zwenergy/CPAK2040/code/msc_disk.c

/*
 * The MIT License (MIT)
 *
 * Copyright (c) 2019 Ha Thach (tinyusb.org)
 *
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
 */
#include "hardware/gpio.h"
#include "bsp/board.h"
#include "tusb_config.h"
#include <stdio.h>

#include "hardware/flash.h"
#include "pico/time.h"


#define MEMPAKSIZE 32768
#define NRMEMPAKS 10
#define BASEMEMPAKADDR ( XIP_BASE + PICO_FLASH_SIZE_BYTES - ( NRMEMPAKS * MEMPAKSIZE ) )
#define MINMOUNTTIME_MS 5000

void writeMemPakToFlash( uint8_t* pak );
extern volatile uint8_t memPakCntr;
extern uint32_t usbReadMode;
void doBlinkPattern( uint32_t count );

// Flag for when a full write happened.
uint32_t fullUSBWriteDone = 0;

#if CFG_TUD_MSC

// whether host does safe-eject
static bool ejected = false;

enum
{
  DISK_BLOCK_NUM_READ = 640,
  DISK_BLOCK_NUM_WRITE = 230,
  DISK_BLOCK_SIZE = 512
};

    // Table for USB READ.
    uint8_t msc_disk_read[5][DISK_BLOCK_SIZE] =
        {
            //------------- Block0: Boot Sector -------------//
            // byte_per_sector    = DISK_BLOCK_SIZE; fat12_sector_num_16  = DISK_BLOCK_NUM;
            // sector_per_cluster = 1; reserved_sectors = 1;
            // fat_num            = 1; fat12_root_entry_num = 16;
            // sector_per_fat     = 1; sector_per_track = 1; head_num = 1; hidden_sectors = 0;
            // drive_number       = 0x80; media_type = 0xf8; extended_boot_signature = 0x29;
            // filesystem_type    = "FAT12   "; volume_serial_number = 0x1234; volume_label = "TinyUSB MSC";
            // FAT magic code at offset 510-511
            {
                // 0,0
                0xEB, 0x3C, 0x90,                               // 0 -2 jump code
                0x4D, 0x53, 0x44, 0x4F, 0x53, 0x35, 0x2E, 0x30, // 3- 10 MSDOS5.0
                0x00, 0x02,                                     // 11-12 BYTES PER SECTOR
                0x04,                                           // 13 SECTORS PER CLUSTER
                0x01, 0x00,                                     // 14-15 Number of reserved sectors
                0x01,                                           // 16 Number of FATs
                0x10, 0x00,                                     // 17-18 max number of root directory enteries
                0x00, 0x20,                                     // 19-20 total number of sectors (set 0 and use 32-35 if large)
                0xF8,                                           // 21 IGNORE
                0x01, 0x00,                                     // 22-23 Sectors per fat
                0x01, 0x00,                                     // 24-25 sectors per track
                0x01, 0x00,                                     // 26-27 number of heads
                0x00, 0x00, 0x00, 0x00,                         // 28-31 IGNORE
                0x00, 0x00, 0x00, 0x00,                         // 32-35 total number of sectors for FAT32, fat 12 and 16 ignore
                0x80,                                           // 36 drive number, IGNORE
                0x00,                                           // 37 IGNORE
                0x29,                                           // 38 This inidicates the next few identifying fields are pressent
                0x34, 0x12, 0x00, 0x00,                         // 39-42 serial number
                'T', 'i', 'n', 'y', 'U',
                'S', 'B', ' ', 'M', 'S', 'C', // 43-53 volume ID

                0x46, 0x41, 0x54, 0x31, 0x32, 0x20, 0x20, 0x20, // 54-61 FILE SYSTEM TYPE (FAT12, FAT16 etc)
                0x00, 0x00,                                     // 62-509 "unused"

                // Zero up to 2 last bytes of FAT magic code
                0x00, 0x00, 0x00, 0x00, 0x00, 0x00, 0x00, 0x00, 0x00, 0x00, 0x00, 0x00, 0x00, 0x00, 0x00, 0x00,
                0x00, 0x00, 0x00, 0x00, 0x00, 0x00, 0x00, 0x00, 0x00, 0x00, 0x00, 0x00, 0x00, 0x00, 0x00, 0x00,
                0x00, 0x00, 0x00, 0x00, 0x00, 0x00, 0x00, 0x00, 0x00, 0x00, 0x00, 0x00, 0x00, 0x00, 0x00, 0x00,
                0x00, 0x00, 0x00, 0x00, 0x00, 0x00, 0x00, 0x00, 0x00, 0x00, 0x00, 0x00, 0x00, 0x00, 0x00, 0x00,
                0x00, 0x00, 0x00, 0x00, 0x00, 0x00, 0x00, 0x00, 0x00, 0x00, 0x00, 0x00, 0x00, 0x00, 0x00, 0x00,
                0x00, 0x00, 0x00, 0x00, 0x00, 0x00, 0x00, 0x00, 0x00, 0x00, 0x00, 0x00, 0x00, 0x00, 0x00, 0x00,
                0x00, 0x00, 0x00, 0x00, 0x00, 0x00, 0x00, 0x00, 0x00, 0x00, 0x00, 0x00, 0x00, 0x00, 0x00, 0x00,
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
                0x00, 0x80, 0x00, 0x00, 

                'M', 'E', 'M', 'P', 'A', 'K', '0', '5', 'M', 'P', 'K', 0x20, 0x00, 0xC6, 0x52, 0x6D,
                0x65, 0x43, 0x65, 0x43, 0x00, 0x00, 0x88, 0x6D, 0x65, 0x43, 0x42, 0x00,
                0x00, 0x80, 0x00, 0x00, 

                'M', 'E', 'M', 'P', 'A', 'K', '0', '6', 'M', 'P', 'K', 0x20, 0x00, 0xC6, 0x52, 0x6D,
                0x65, 0x43, 0x65, 0x43, 0x00, 0x00, 0x88, 0x6D, 0x65, 0x43, 0x52, 0x00,
                0x00, 0x80, 0x00, 0x00, 

                'M', 'E', 'M', 'P', 'A', 'K', '0', '7', 'M', 'P', 'K', 0x20, 0x00, 0xC6, 0x52, 0x6D,
                0x65, 0x43, 0x65, 0x43, 0x00, 0x00, 0x88, 0x6D, 0x65, 0x43, 0x62, 0x00,
                0x00, 0x80, 0x00, 0x00, 

                'M', 'E', 'M', 'P', 'A', 'K', '0', '8', 'M', 'P', 'K', 0x20, 0x00, 0xC6, 0x52, 0x6D,
                0x65, 0x43, 0x65, 0x43, 0x00, 0x00, 0x88, 0x6D, 0x65, 0x43, 0x72, 0x00,
                0x00, 0x80, 0x00, 0x00, 

                'M', 'E', 'M', 'P', 'A', 'K', '0', '9', 'M', 'P', 'K', 0x20, 0x00, 0xC6, 0x52, 0x6D,
                0x65, 0x43, 0x65, 0x43, 0x00, 0x00, 0x88, 0x6D, 0x65, 0x43, 0x82, 0x00,
                0x00, 0x80, 0x00, 0x00, 

                'M', 'E', 'M', 'P', 'A', 'K', '1', '0', 'M', 'P', 'K', 0x20, 0x00, 0xC6, 0x52, 0x6D,
                0x65, 0x43, 0x65, 0x43, 0x00, 0x00, 0x88, 0x6D, 0x65, 0x43, 0x82, 0x00,
                0x00, 0x80, 0x00, 0x00,
                
            },
            //------------- Block3: -------------// 3,0
};

        // Table for USB WRITE
        uint8_t msc_disk_write[5][DISK_BLOCK_SIZE] =
        {
            //------------- Block0: Boot Sector -------------//
            // byte_per_sector    = DISK_BLOCK_SIZE; fat12_sector_num_16  = DISK_BLOCK_NUM;
            // sector_per_cluster = 1; reserved_sectors = 1;
            // fat_num            = 1; fat12_root_entry_num = 16;
            // sector_per_fat     = 1; sector_per_track = 1; head_num = 1; hidden_sectors = 0;
            // drive_number       = 0x80; media_type = 0xf8; extended_boot_signature = 0x29;
            // filesystem_type    = "FAT12   "; volume_serial_number = 0x1234; volume_label = "TinyUSB MSC";
            // FAT magic code at offset 510-511
            {
                // 0,0
                0xEB, 0x3C, 0x90,                               // 0 -2 jump code
                0x4D, 0x53, 0x44, 0x4F, 0x53, 0x35, 0x2E, 0x30, // 3- 10 MSDOS5.0
                0x00, 0x02,                                     // 11-12 BYTES PER SECTOR
                0x04,                                           // 13 SECTORS PER CLUSTER
                0x01, 0x00,                                     // 14-15 Number of reserved sectors
                0x01,                                           // 16 Number of FATs
                0x10, 0x00,                                     // 17-18 max number of root directory enteries
                DISK_BLOCK_NUM_WRITE, 0x00,                                     // 19-20 total number of sectors (set 0 and use 32-35 if large)
                0xF8,                                           // 21 IGNORE
                0x01, 0x00,                                     // 22-23 Sectors per fat
                0x01, 0x00,                                     // 24-25 sectors per track
                0x01, 0x00,                                     // 26-27 number of heads
                0x00, 0x00, 0x00, 0x00,                         // 28-31 IGNORE
                0x00, 0x00, 0x00, 0x00,                         // 32-35 total number of sectors for FAT32, fat 12 and 16 ignore
                0x80,                                           // 36 drive number, IGNORE
                0x00,                                           // 37 IGNORE
                0x29,                                           // 38 This inidicates the next few identifying fields are pressent
                0x34, 0x12, 0x00, 0x00,                         // 39-42 serial number
                'T', 'i', 'n', 'y', 'U',
                'S', 'B', ' ', 'M', 'S', 'C', // 43-53 volume ID


                0x46, 0x41, 0x54, 0x31, 0x32, 0x20, 0x20, 0x20, // 54-61 FILE SYSTEM TYPE (FAT12, FAT16 etc)
                0x00, 0x00,                                     // 62-509 "unused"

                // Zero up to 2 last bytes of FAT magic code
                0x00, 0x00, 0x00, 0x00, 0x00, 0x00, 0x00, 0x00, 0x00, 0x00, 0x00, 0x00, 0x00, 0x00, 0x00, 0x00,
                0x00, 0x00, 0x00, 0x00, 0x00, 0x00, 0x00, 0x00, 0x00, 0x00, 0x00, 0x00, 0x00, 0x00, 0x00, 0x00,
                0x00, 0x00, 0x00, 0x00, 0x00, 0x00, 0x00, 0x00, 0x00, 0x00, 0x00, 0x00, 0x00, 0x00, 0x00, 0x00,
                0x00, 0x00, 0x00, 0x00, 0x00, 0x00, 0x00, 0x00, 0x00, 0x00, 0x00, 0x00, 0x00, 0x00, 0x00, 0x00,
                0x00, 0x00, 0x00, 0x00, 0x00, 0x00, 0x00, 0x00, 0x00, 0x00, 0x00, 0x00, 0x00, 0x00, 0x00, 0x00,
                0x00, 0x00, 0x00, 0x00, 0x00, 0x00, 0x00, 0x00, 0x00, 0x00, 0x00, 0x00, 0x00, 0x00, 0x00, 0x00,
                0x00, 0x00, 0x00, 0x00, 0x00, 0x00, 0x00, 0x00, 0x00, 0x00, 0x00, 0x00, 0x00, 0x00, 0x00, 0x00,
                0x00, 0x00, 0x00, 0x00, 0x00, 0x00, 0x00, 0x00, 0x00, 0x00, 0x00, 0x00, 0x00, 0x00, 0x00, 0x00,

                0x00, 0x00, 0x00, 0x00, 0x00, 0x00, 0x00, 0x00, 0x00, 0x00, 0x00, 0x00, 0x00, 0x00, 0x00, 0x00,
                0x00, 0x00, 0x00, 0x00, 0x00, 0x00, 0x00, 0x00, 0x00, 0x00, 0x00, 0x00, 0x00, 0x00, 0x00, 0x00,
                0x00, 0x00, 0x00, 0x00, 0x00, 0x00, 0x00, 0x00, 0x00, 0x00, 0x00, 0x00, 0x00, 0x00, 0x00, 0x00,
                0x00, 0x00, 0x00, 0x00, 0x00, 0x00, 0x00, 0x00, 0x00, 0x00, 0x00, 0x00, 0x00, 0x00, 0x00, 0x00,
                0x00, 0x00, 0x00, 0x00, 0x00, 0x00, 0x00, 0x00, 0x00, 0x00, 0x00, 0x00, 0x00, 0x00, 0x00, 0x00,
                0x00, 0x00, 0x00, 0x00, 0x00, 0x00, 0x00, 0x00, 0x00, 0x00, 0x00, 0x00, 0x00, 0x00, 0x00, 0x00,
                0x00, 0x00, 0x00, 0x00, 0x00, 0x00, 0x00, 0x00, 0x00, 0x00, 0x00, 0x00, 0x00, 0x00, 0x00, 0x00,
                0x00, 0x00, 0x00, 0x00, 0x00, 0x00, 0x00, 0x00, 0x00, 0x00, 0x00, 0x00, 0x00, 0x00, 0x00, 0x00,

                0x00, 0x00, 0x00, 0x00, 0x00, 0x00, 0x00, 0x00, 0x00, 0x00, 0x00, 0x00, 0x00, 0x00, 0x00, 0x00,
                0x00, 0x00, 0x00, 0x00, 0x00, 0x00, 0x00, 0x00, 0x00, 0x00, 0x00, 0x00, 0x00, 0x00, 0x00, 0x00,
                0x00, 0x00, 0x00, 0x00, 0x00, 0x00, 0x00, 0x00, 0x00, 0x00, 0x00, 0x00, 0x00, 0x00, 0x00, 0x00,
                0x00, 0x00, 0x00, 0x00, 0x00, 0x00, 0x00, 0x00, 0x00, 0x00, 0x00, 0x00, 0x00, 0x00, 0x00, 0x00,
                0x00, 0x00, 0x00, 0x00, 0x00, 0x00, 0x00, 0x00, 0x00, 0x00, 0x00, 0x00, 0x00, 0x00, 0x00, 0x00,
                0x00, 0x00, 0x00, 0x00, 0x00, 0x00, 0x00, 0x00, 0x00, 0x00, 0x00, 0x00, 0x00, 0x00, 0x00, 0x00,
                0x00, 0x00, 0x00, 0x00, 0x00, 0x00, 0x00, 0x00, 0x00, 0x00, 0x00, 0x00, 0x00, 0x00, 0x00, 0x00,
                0x00, 0x00, 0x00, 0x00, 0x00, 0x00, 0x00, 0x00, 0x00, 0x00, 0x00, 0x00, 0x00, 0x00, 0x00, 0x00,

                0x00, 0x00, 0x00, 0x00, 0x00, 0x00, 0x00, 0x00, 0x00, 0x00, 0x00, 0x00, 0x00, 0x00, 0x00, 0x00,
                0x00, 0x00, 0x00, 0x00, 0x00, 0x00, 0x00, 0x00, 0x00, 0x00, 0x00, 0x00, 0x00, 0x00, 0x00, 0x00,
                0x00, 0x00, 0x00, 0x00, 0x00, 0x00, 0x00, 0x00, 0x00, 0x00, 0x00, 0x00, 0x00, 0x00, 0x00, 0x00,
                0x00, 0x00, 0x00, 0x00, 0x00, 0x00, 0x00, 0x00, 0x00, 0x00, 0x00, 0x00, 0x00, 0x00, 0x55, 0xAA
            },

            //------------- Block1: FAT12 Table -------------//
            {
                0xF8, 0xFF, 0xFF,

                0x03, 0x40, 0x00,
                0x05, 0x60, 0x00,
                0x07, 0x80, 0x00,
                0x09, 0xa0, 0x00,
                0x0b, 0xc0, 0x00,
                0x0d, 0xe0, 0x00,
                0x0f, 0x00, 0x01,
                0x11, 0xf0, 0xff,
                

            },
            //------------- Block2: Root Directory -------------// 2,0
            {
                // first entry is volume label
                'C', 'P', 'A', 'K', '2', '0', '4', '0', ' ', ' ', ' ', 0x08, 0x00, 0x00, 0x00, 0x00,
                0x00, 0x00, 0x00, 0x00, 0x00, 0x00, 0x4F, 0x6D, 0x65, 0x43, 0x00, 0x00, 0x00, 0x00, 0x00, 0x00,

                'M', 'E', 'M', 'P', 'A', 'K', ' ', ' ', 'M', 'P', 'K', 0x20, 0x00, 0xC6, 0x52, 0x6D,
                0x65, 0x43, 0x65, 0x43, 0x00, 0x00, 0x88, 0x6D, 0x65, 0x43, 0x02, 0x00,
                0x00, 0x80, 0x00, 0x00,

                
            },
            //------------- Block3: -------------// 3,0
};


// Invoked when received SCSI_CMD_INQUIRY
// Application fill vendor id, product id and revision with string up to 8, 16, 4 characters respectively
void tud_msc_inquiry_cb(uint8_t lun, uint8_t vendor_id[8], uint8_t product_id[16], uint8_t product_rev[4])
{
  (void)lun;

  const char vid[] = "TinyUSB";
  const char pid[] = "Mass Storage";
  const char rev[] = "1.0";

  memcpy(vendor_id, vid, strlen(vid));
  memcpy(product_id, pid, strlen(pid));
  memcpy(product_rev, rev, strlen(rev));
}

// Invoked when received Test Unit Ready command.
// return true allowing host to read/write this LUN e.g SD card inserted
bool tud_msc_test_unit_ready_cb(uint8_t lun)
{
  (void)lun;

  // RAM disk is ready until ejected
  if (ejected)
  {
    tud_msc_set_sense(lun, SCSI_SENSE_NOT_READY, 0x3a, 0x00);
    return false;
  }

  return true;
}

// Invoked when received SCSI_CMD_READ_CAPACITY_10 and SCSI_CMD_READ_FORMAT_CAPACITY to determine the disk size
// Application update block count and block size
void tud_msc_capacity_cb(uint8_t lun, uint32_t *block_count, uint16_t *block_size)
{
  (void)lun;
  
  if ( usbReadMode ) {
    *block_count = DISK_BLOCK_NUM_READ;
  } else {
    *block_count = DISK_BLOCK_NUM_WRITE;
  }

  *block_size = DISK_BLOCK_SIZE;
}

// Invoked when received Start Stop Unit command
// - Start = 0 : stopped power mode, if load_eject = 1 : unload disk storage
// - Start = 1 : active mode, if load_eject = 1 : load disk storage
bool tud_msc_start_stop_cb(uint8_t lun, uint8_t power_condition, bool start, bool load_eject)
{
  (void)lun;
  (void)power_condition;

  if (load_eject)
  {
    if (start)
    {
      // load disk storage
    }
    else
    {
      // unload disk storage
      ejected = true;
    }
  }

  return true;
}

// Callback invoked when received READ10 command.
// Copy disk's data to buffer (up to bufsize) and return number of copied bytes.
int32_t tud_msc_read10_cb(uint8_t lun, uint32_t lba, uint32_t offset, void *buffer, uint32_t bufsize)
{
  (void)lun;
  
  uint8_t *addr;

  // Re-direct reads to the data directly to the Flash.
  if ( lba < 3 ) {
    addr = ( usbReadMode ?  msc_disk_read[ lba ] : msc_disk_write[ lba ] ) + offset;
  } else {
    addr = (uint8_t*) BASEMEMPAKADDR + ( ( lba - 3 ) * DISK_BLOCK_SIZE ) + offset;
    
    if ( !usbReadMode ) {
      addr += memPakCntr * MEMPAKSIZE;
    }
  }

  memcpy(buffer, addr, bufsize);

  return bufsize;
}

bool tud_msc_is_writable_cb(uint8_t lun)
{
  (void)lun;
  
  if ( usbReadMode ) {
    return false;
  } else {
    return true;
  }
}


// Temporary write buffer.
uint8_t writeBuffer[ MEMPAKSIZE * 2 ];
uint32_t offsetCnt = 0;
uint32_t didFlash = 0;

// Callback invoked when received WRITE10 command.
// Process data in buffer to disk's storage and return number of written bytes
int32_t tud_msc_write10_cb(uint8_t lun, uint32_t lba, uint32_t offset, uint8_t* buffer, uint32_t bufsize)
{
  (void) lun;
  
  if ( usbReadMode ) {
    return -1;
  }
  
  if ( lba >= DISK_BLOCK_NUM_WRITE )
    return -1;
  
  if ( lba >= 3 ) {
    // Actual data write.
      memcpy( writeBuffer + offsetCnt, buffer, bufsize );
      offsetCnt += bufsize;
      
  } else if ( lba == 2 ) {
    // Check if the offset cnt is right.
    if ( offsetCnt == MEMPAKSIZE && !didFlash ) {
      writeMemPakToFlash( writeBuffer );
      fullUSBWriteDone = to_ms_since_boot( get_absolute_time() );
      didFlash = 1;
    }
    
    offsetCnt = 0;
  }

  return (int32_t) bufsize;
}

// Callback invoked when received an SCSI command not in built-in list below
// - READ_CAPACITY10, READ_FORMAT_CAPACITY, INQUIRY, MODE_SENSE6, REQUEST_SENSE
// - READ10 and WRITE10 has their own callbacks
int32_t tud_msc_scsi_cb(uint8_t lun, uint8_t const scsi_cmd[16], void *buffer, uint16_t bufsize)
{
  // read10 & write10 has their own callback and MUST not be handled here

  void const *response = NULL;
  int32_t resplen = 0;

  // most scsi handled is input
  bool in_xfer = true;

  switch (scsi_cmd[0])
  {
  case SCSI_CMD_PREVENT_ALLOW_MEDIUM_REMOVAL:
    // Host is about to read/write etc ... better not to disconnect disk
    resplen = 0;
    break;

  default:
    // Set Sense = Invalid Command Operation
    tud_msc_set_sense(lun, SCSI_SENSE_ILLEGAL_REQUEST, 0x20, 0x00);

    // negative means error -> tinyusb could stall and/or response with failed status
    resplen = -1;
    break;
  }

  // return resplen must not larger than bufsize
  if (resplen > bufsize)
    resplen = bufsize;

  if (response && (resplen > 0))
  {
    if (in_xfer)
    {
      memcpy(buffer, response, resplen);
    }
    else
    {
      // SCSI output
    }
  }

  return resplen;
}

#endif
